ThunderFly-aerospace/Auto-G2/CAD/img/111_1009.png

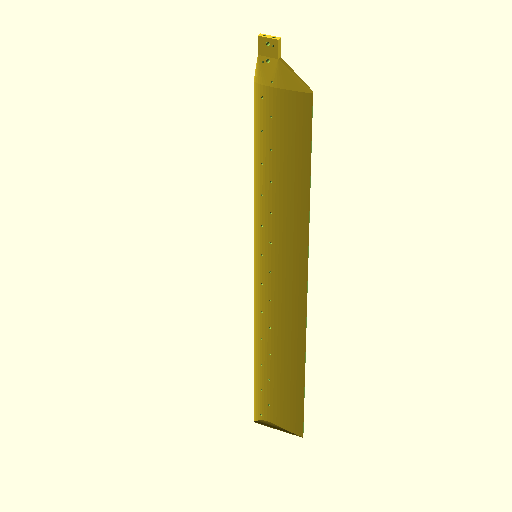
CAD/img/111_1009.png
