ThunderFly-aerospace/Auto-G2/CAD/img/888_1010.png

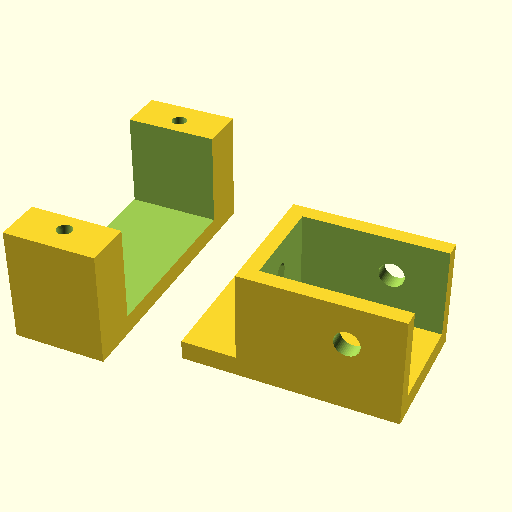
CAD/img/888_1010.png
