ThunderFly-aerospace/Auto-G2/doc/img/111_1001.png

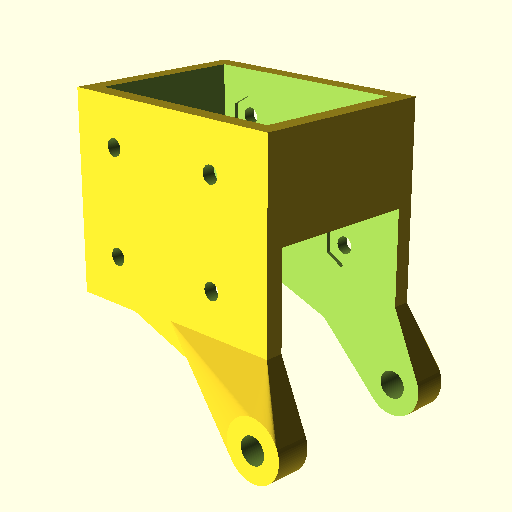
doc/img/111_1001.png
