ThunderFly-aerospace/Auto-G2/doc/img/111_1002.png

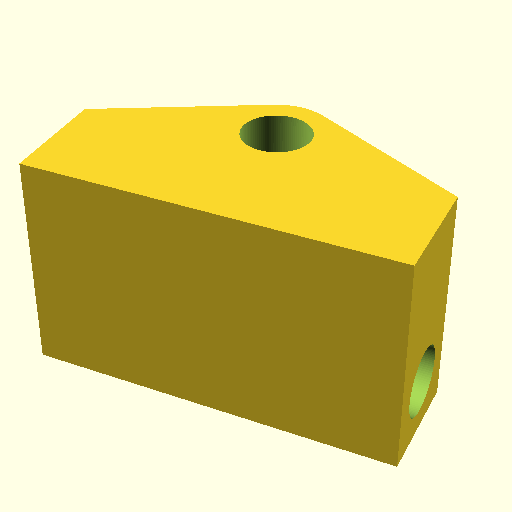
doc/img/111_1002.png
