ThunderFly-aerospace/Auto-G2/doc/img/111_1003.png

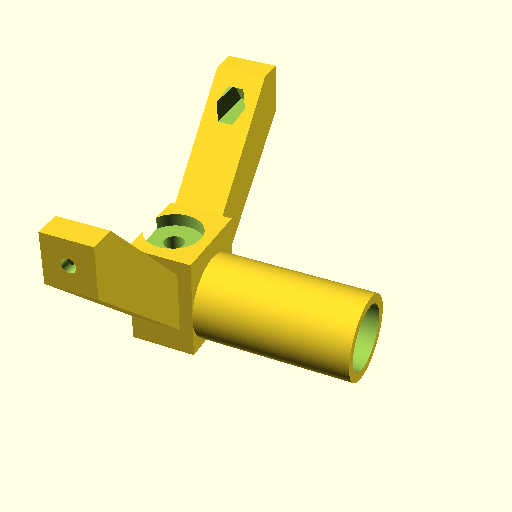
doc/img/111_1003.png
