ThunderFly-aerospace/Auto-G2/doc/img/111_1004.png

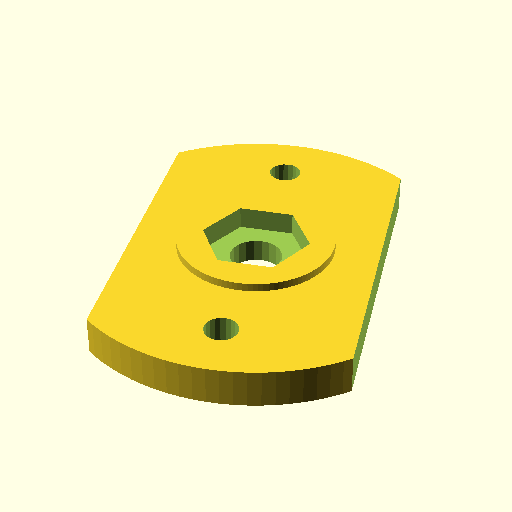
doc/img/111_1004.png
