ThunderFly-aerospace/Auto-G2/doc/img/111_1005.png

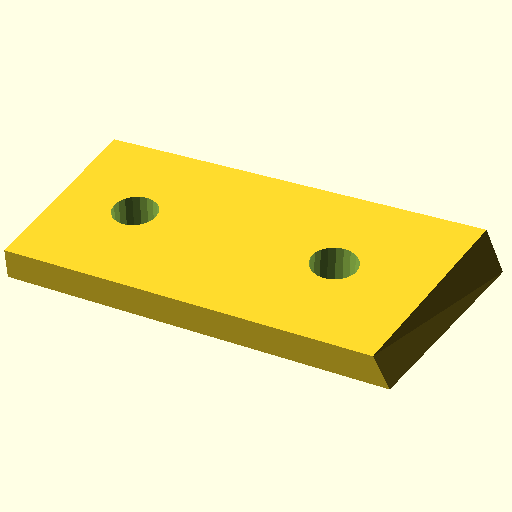
doc/img/111_1005.png
