ThunderFly-aerospace/Auto-G2/doc/img/111_1006.png

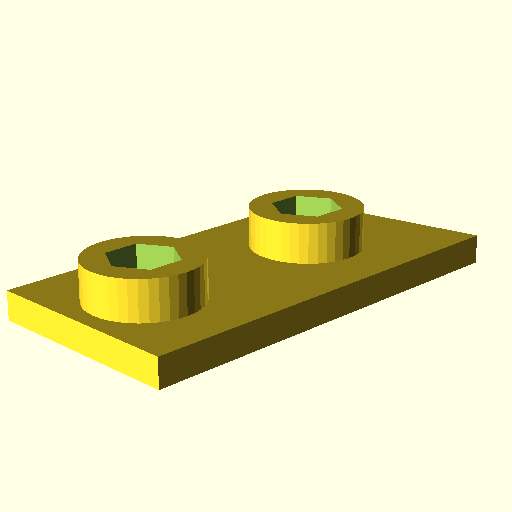
doc/img/111_1006.png
