ThunderFly-aerospace/Auto-G2/doc/img/111_1007.png

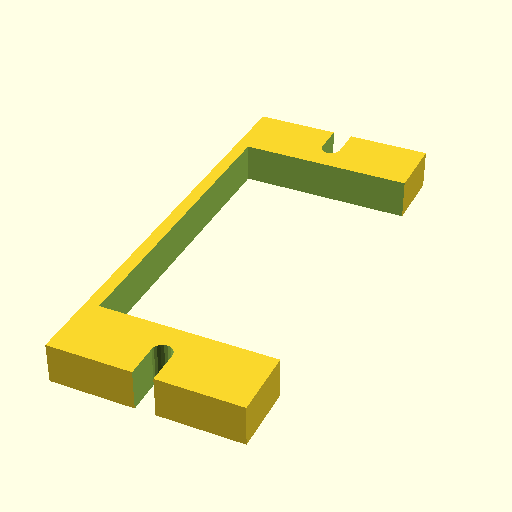
doc/img/111_1007.png
