ThunderFly-aerospace/Auto-G2/doc/img/111_1008.png

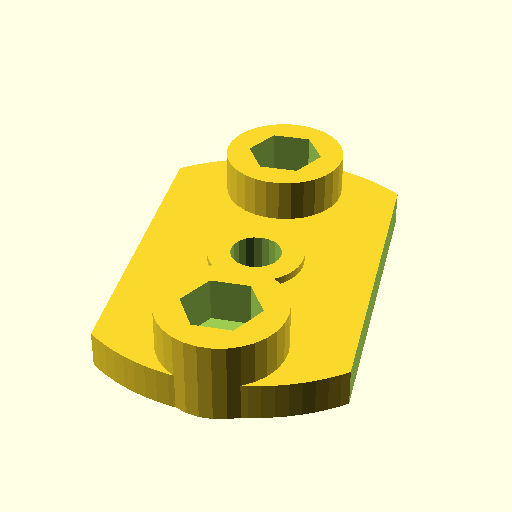
doc/img/111_1008.png
