ThunderFly-aerospace/Auto-G2/doc/img/111_1009.png

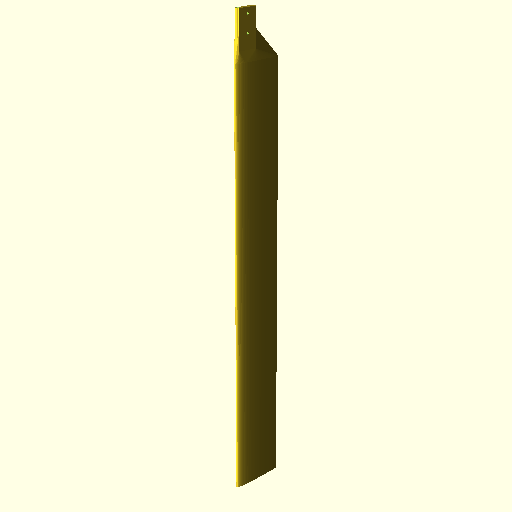
doc/img/111_1009.png
