ThunderFly-aerospace/Auto-G2/doc/img/111_1101.png

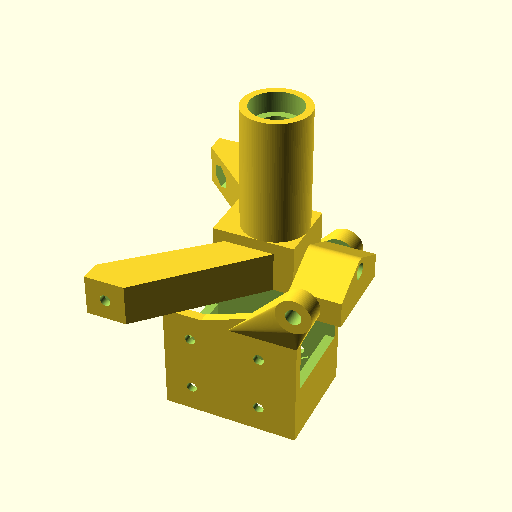
doc/img/111_1101.png
