ThunderFly-aerospace/Auto-G2/doc/img/111_1102.png

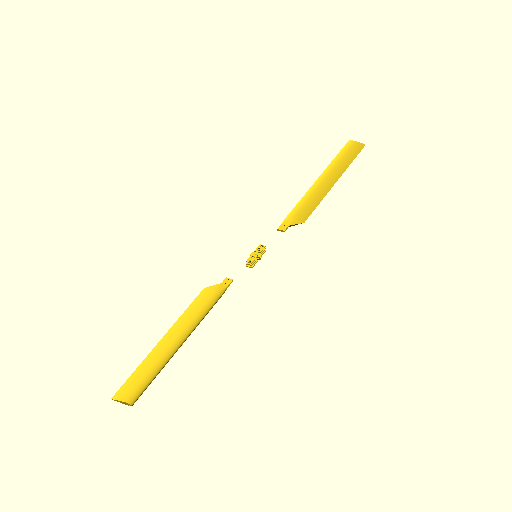
doc/img/111_1102.png
