ThunderFly-aerospace/Auto-G2/doc/img/888_1001.png

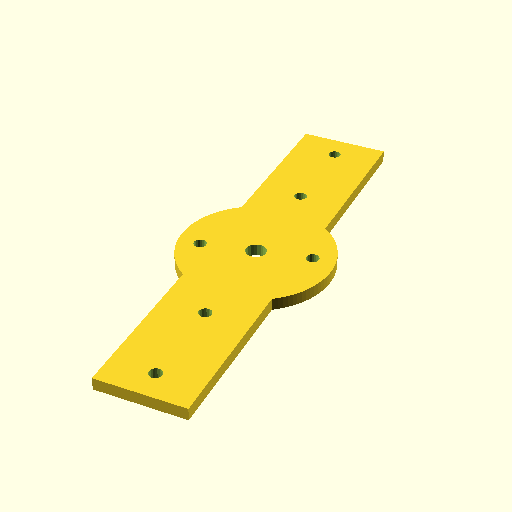
doc/img/888_1001.png
