ThunderFly-aerospace/Auto-G2/doc/img/888_1002.png

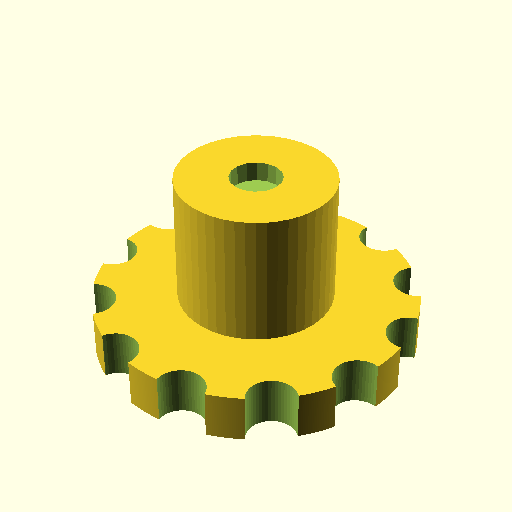
doc/img/888_1002.png
