ThunderFly-aerospace/Auto-G2/doc/img/888_1003.png

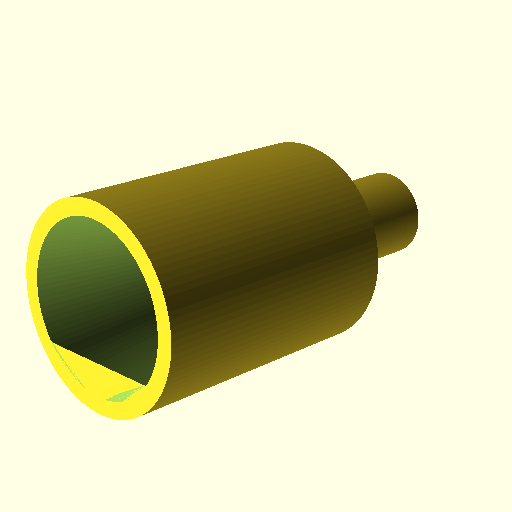
doc/img/888_1003.png
