ThunderFly-aerospace/Auto-G2/doc/img/888_1009.png

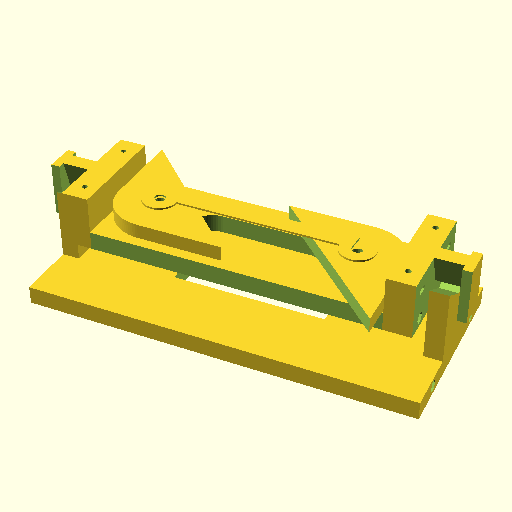
doc/img/888_1009.png
