ThunderFly-aerospace/Auto-G2/doc/img/888_1011.png

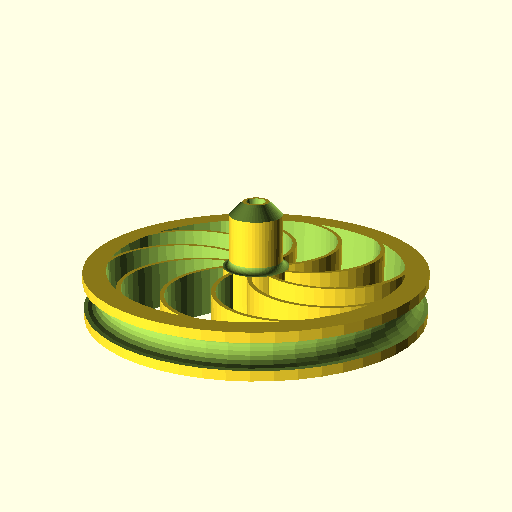
doc/img/888_1011.png
