ThunderFly-aerospace/Auto-G2/doc/img/20190310_154213.jpg

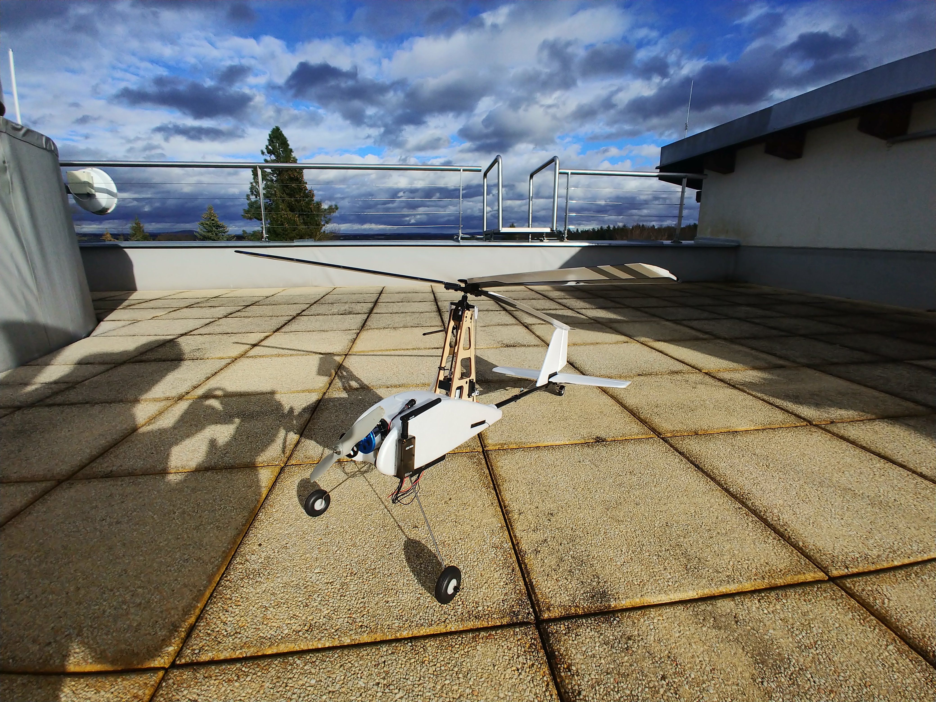
doc/img/20190310_154213.jpg
