ThunderFly-aerospace/Auto-G2/doc/wiki/meshlab_1.png

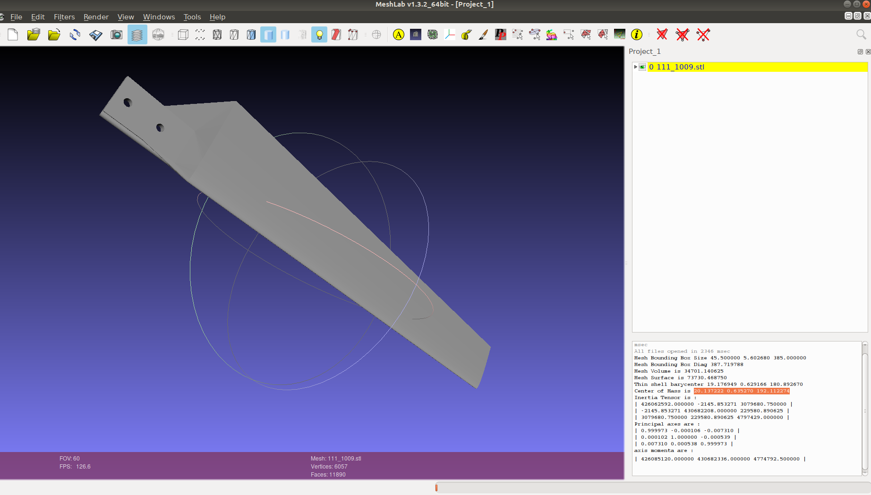
doc/wiki/meshlab_1.png
