ThunderFly-aerospace/Auto-G2/CAD/img/print_plate_rotor_parts.png

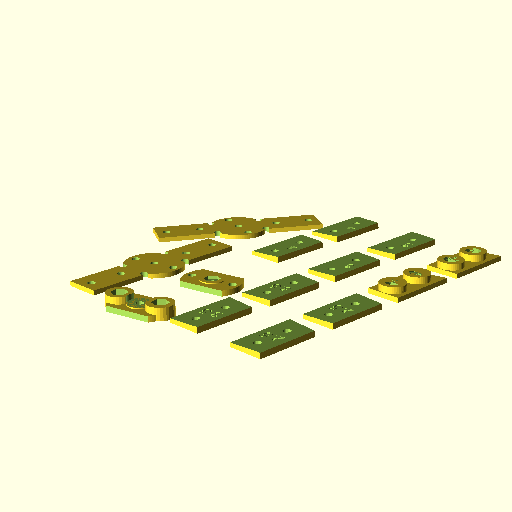
CAD/img/print_plate_rotor_parts.png
