ThunderFly-aerospace/Auto-G2/doc/img/111_1009_parts.png

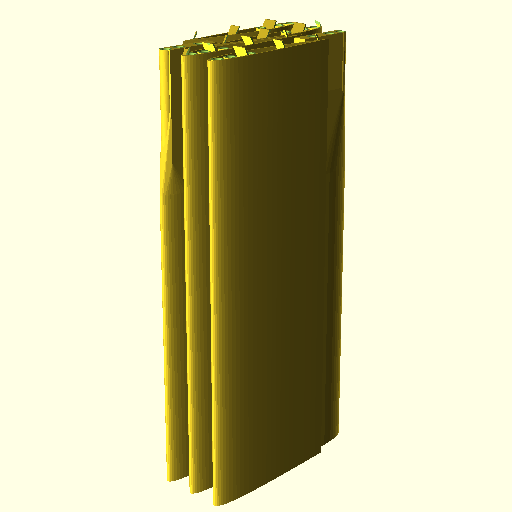
doc/img/111_1009_parts.png
