ThunderFly-aerospace/Auto-G2/doc/img/print_plate_blades_parts.png

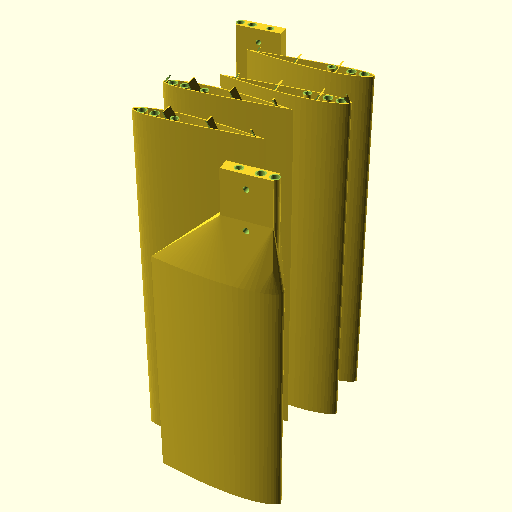
doc/img/print_plate_blades_parts.png
