ThunderFly-aerospace/Auto-G2/CAD/stl/print_plate_888_1001.stl

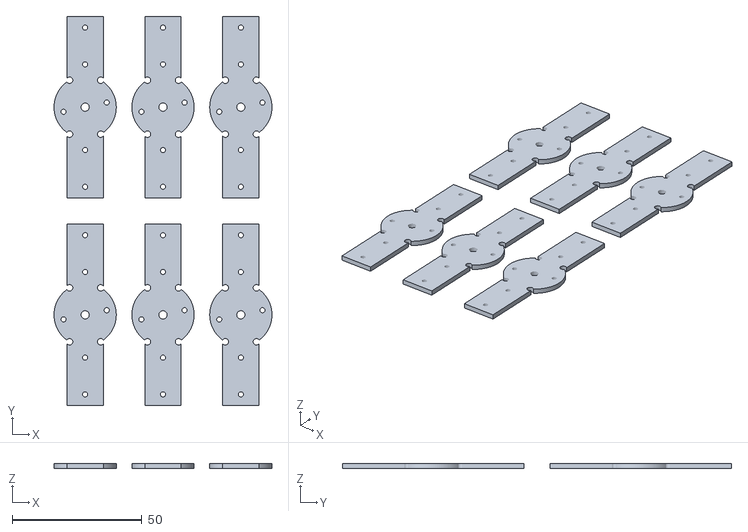
[picture p41: CAD file, 2019-07-24]
CAD/stl/print_plate_888_1001.stl
84.0 x 150.0 x 1.90
