ThunderFly-aerospace/Auto-G2/CAD/stl/888_1011.stl

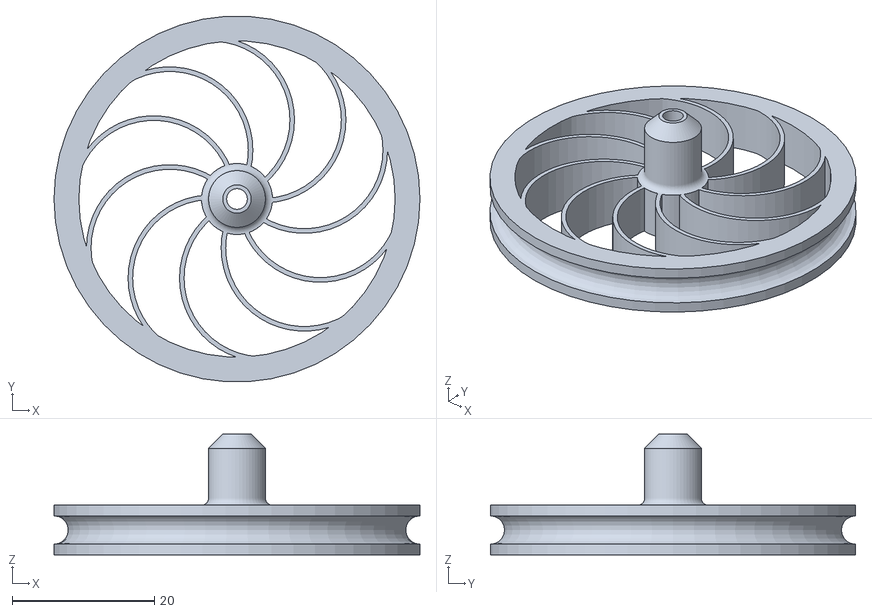
[picture p42: CAD file, 2019-07-24]
CAD/stl/888_1011.stl
51.5 x 51.4 x 17.0
