ThunderFly-aerospace/Auto-G2/CAD/stl/111_1006.stl

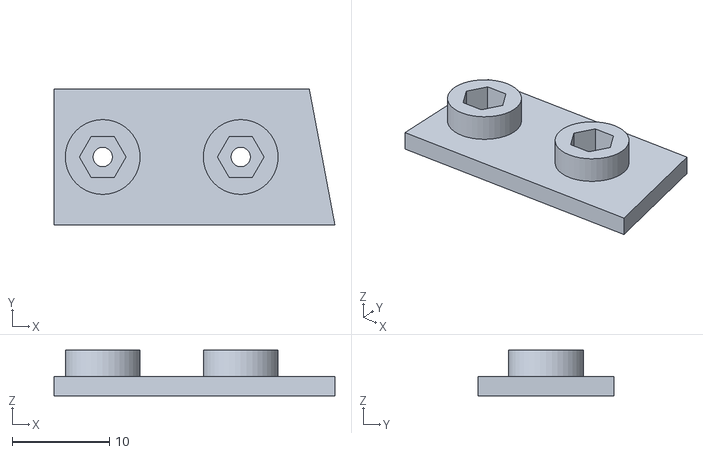
[picture p43: CAD file, 2019-07-04]
CAD/stl/111_1006.stl
28.8 x 14.0 x 4.67
