ThunderFly-aerospace/Auto-G2/CAD/stl/888_1001.stl

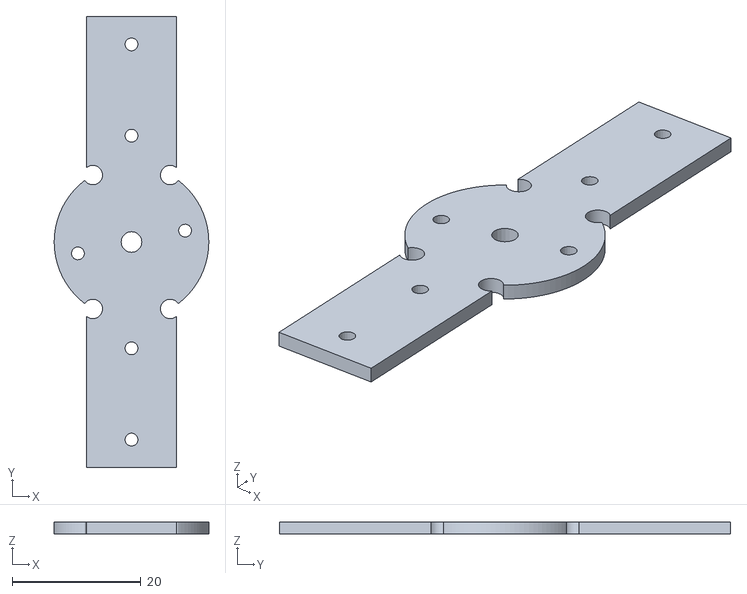
[picture p44: CAD file, 2019-07-04]
CAD/stl/888_1001.stl
24.0 x 70.0 x 1.90
