ThunderFly-aerospace/Auto-G2/CAD/stl/111_1101.stl

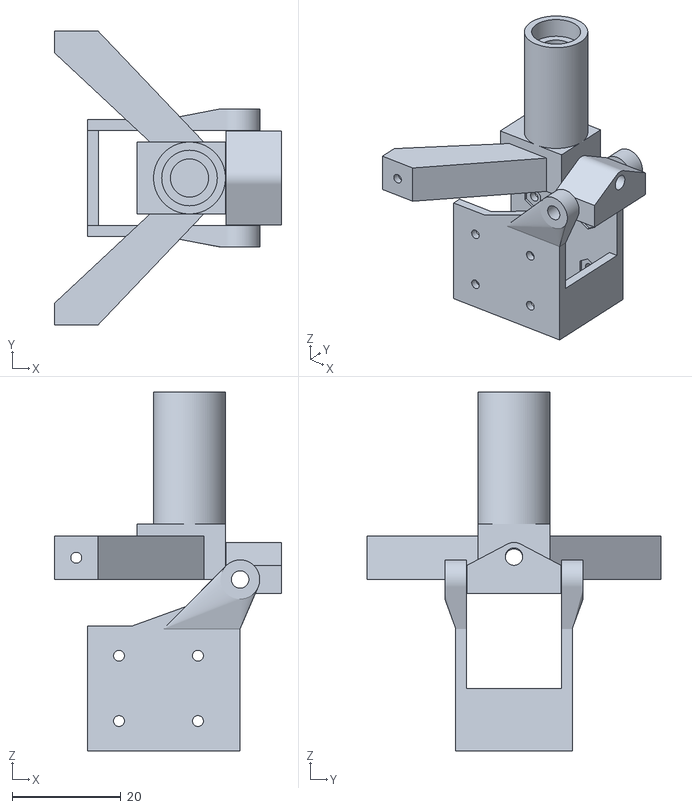
[picture p45: CAD file, 2019-07-04]
CAD/stl/111_1101.stl
41.7 x 54.0 x 65.9
