ThunderFly-aerospace/Auto-G2/CAD/STL/111_1009_parts.stl

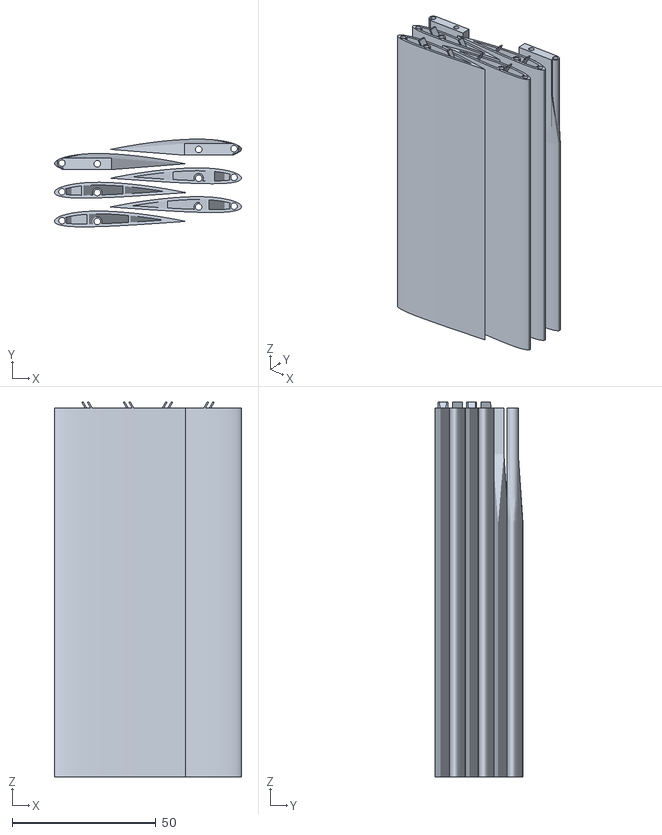
[picture p46: CAD file, 2019-06-12]
CAD/STL/111_1009_parts.stl
65.0 x 30.5 x 130.3
