ThunderFly-aerospace/Auto-G2/CAD/stl/888_1003.stl

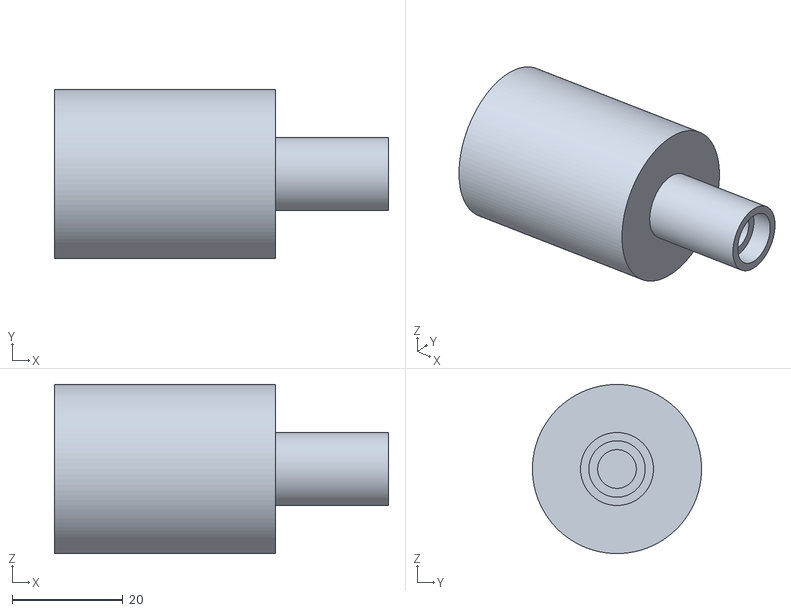
[picture p47: CAD file, 2019-05-24]
CAD/stl/888_1003.stl
60.4 x 30.6 x 30.6
