ThunderFly-aerospace/Auto-G2/CAD/stl/111_1003.stl

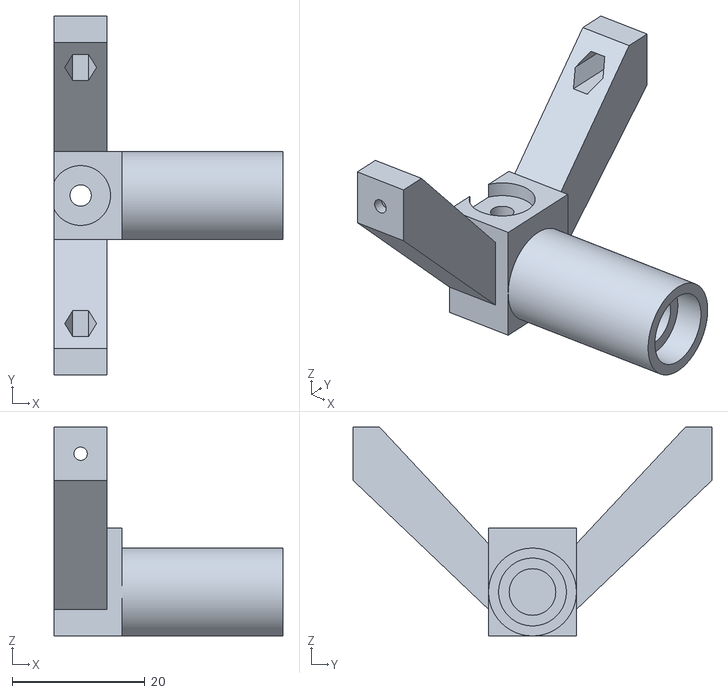
[picture p48: CAD file, 2019-05-24]
CAD/stl/111_1003.stl
34.4 x 54.0 x 31.4
