ThunderFly-aerospace/Auto-G2/CAD/stl/111_1001.stl

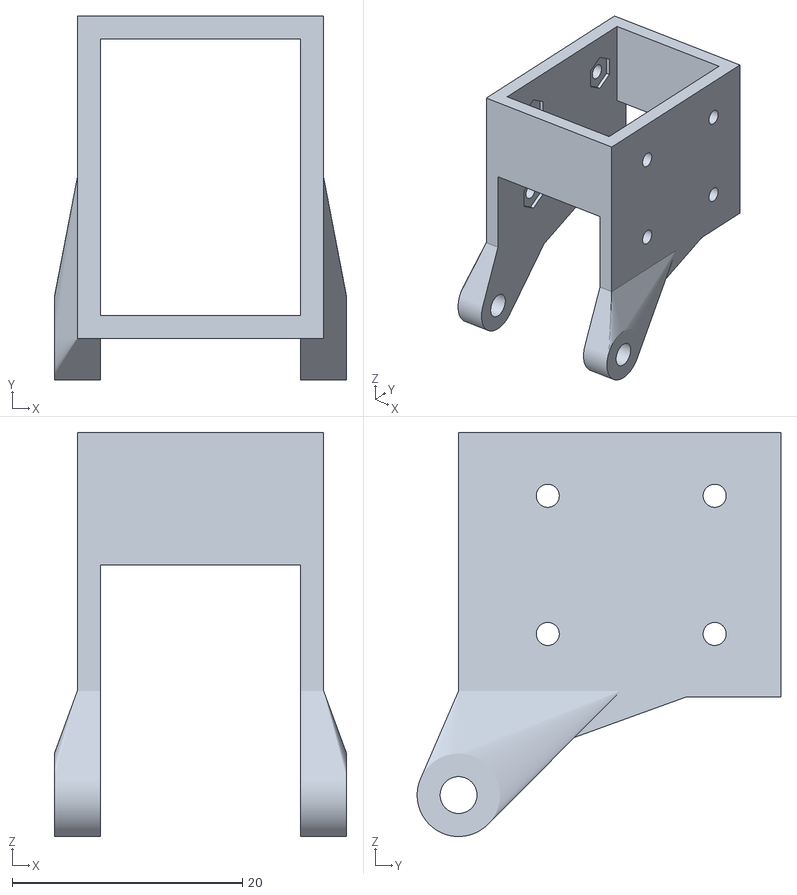
[picture p49: CAD file, 2019-05-24]
CAD/stl/111_1001.stl
25.4 x 31.6 x 35.1
