ThunderFly-aerospace/Auto-G2/CAD/stl/111_1005.stl

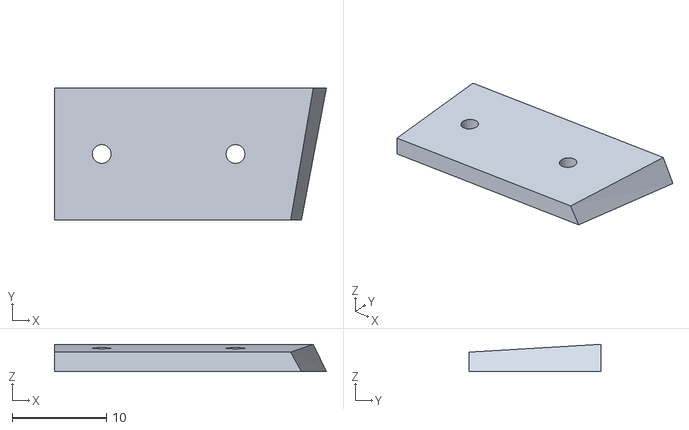
[picture p50: CAD file, 2019-05-24]
CAD/stl/111_1005.stl
28.8 x 14.0 x 2.90
