ThunderFly-aerospace/Auto-G2/CAD/stl/888_1002.stl

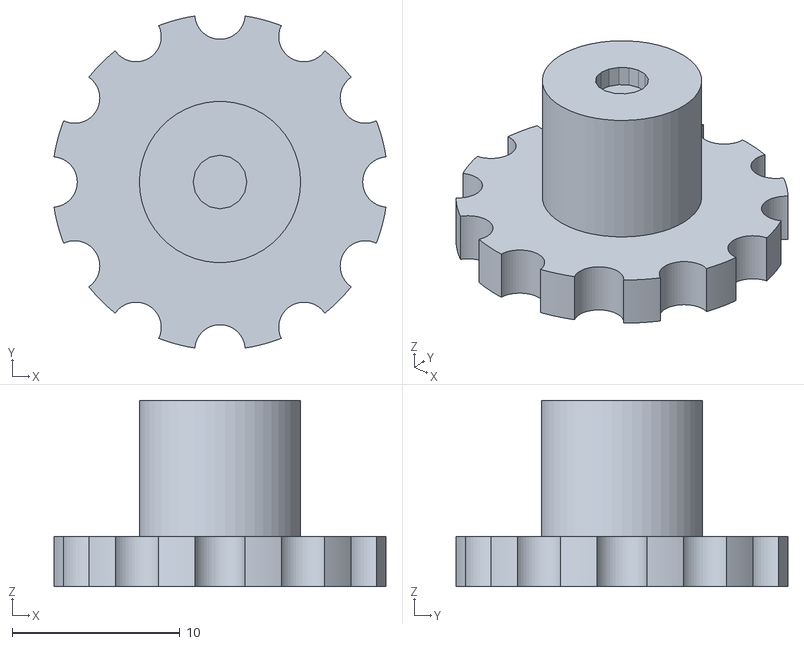
[picture p51: CAD file, 2019-05-06]
CAD/stl/888_1002.stl
19.8 x 19.8 x 11.1
