ThunderFly-aerospace/Auto-G2/CAD/stl/888_1009.stl

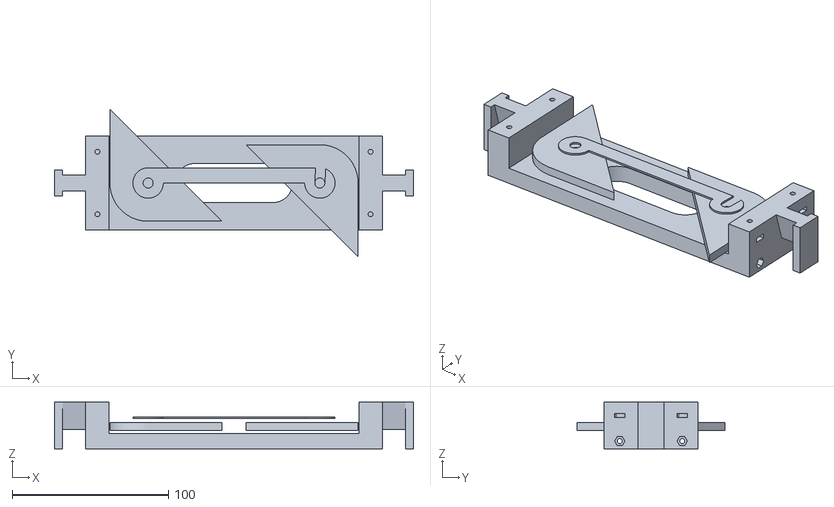
[picture p52: CAD file, 2019-05-06]
CAD/stl/888_1009.stl
230.0 x 94.7 x 30.0
