ThunderFly-aerospace/Auto-G2/CAD/stl/111_1007.stl

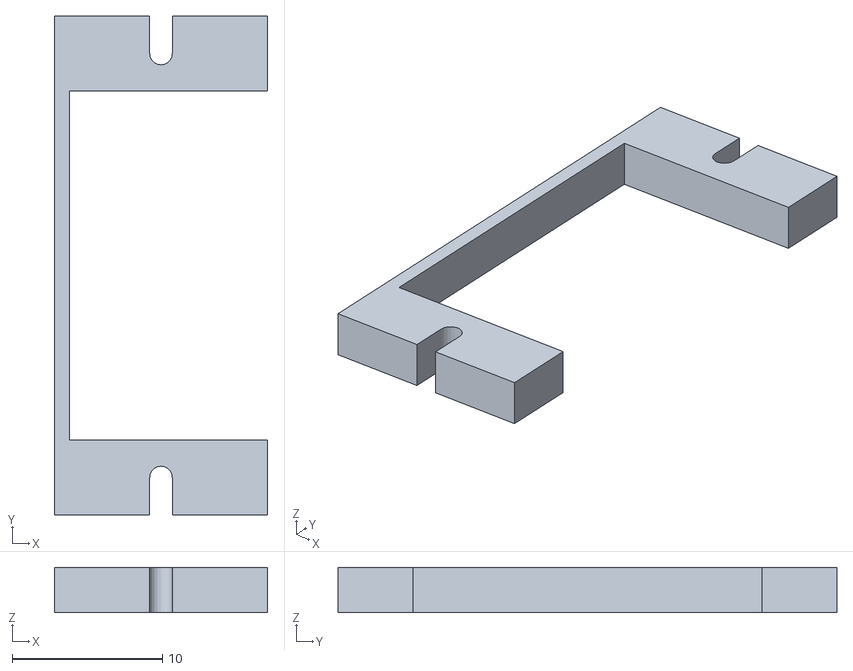
[picture p53: CAD file, 2019-04-24]
CAD/stl/111_1007.stl
14.2 x 33.2 x 3.00
