ThunderFly-aerospace/Auto-G2/CAD/STL/111_1102.stl

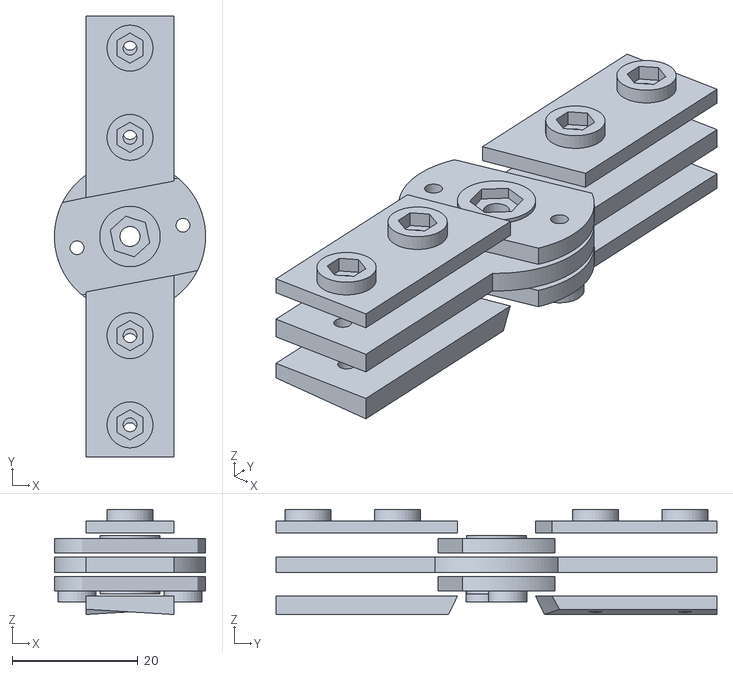
[picture p54: CAD file, 2019-04-24]
CAD/STL/111_1102.stl
24.0 x 70.0 x 16.7
