ThunderFly-aerospace/Auto-G2/CAD/stl/111_1002.stl

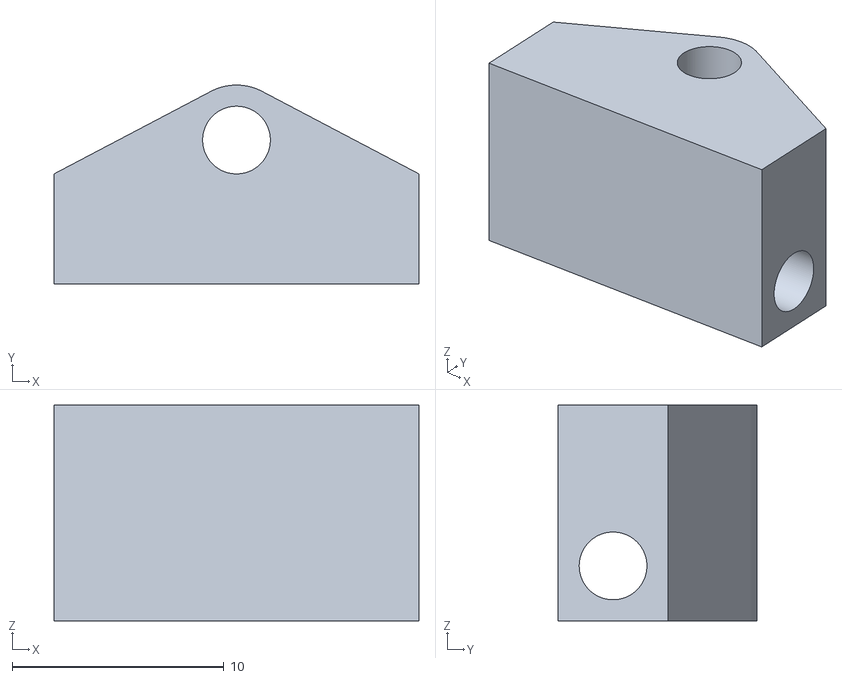
[picture p55: CAD file, 2019-03-27]
CAD/stl/111_1002.stl
17.2 x 9.40 x 10.2
