ThunderFly-aerospace/Auto-G2/CAD/src/888_1001.scad

//
//
//

include <../parameters.scad>

module 888_1001(hole_diameter=3)
{
    angle_between_blades = 360 / rotor_blades_count;
    rotor_center_plate_size = 30;
    rotor_mounting_plate_size = 20;
    shaft_diameter = M3_screw_diameter;
    thickness = 1.9;
    blade_screws_distance = (16.47+11.86)/2;

    translate([0, 0, thickness/2])
    difference () {
        union () {
            cylinder(r = 3+9, h = thickness, center = true, $fn = 100);

            for (i = [0:rotor_blades_count]){
                rotate([0,0, i*angle_between_blades])
                    translate([0, 20, 0])
                        cube([14, 30, thickness], center = true);
            }
        }

        cylinder(d = shaft_diameter, h = 2* thickness, center = true, $fn = 20);


        for (i = [1:rotor_blades_count]){
            rotate([0,0, i*angle_between_blades])
                translate([0, 16.5 + blade_screws_distance/2, 0]) {
                    translate([0, blade_screws_distance/2, 0])
                        cylinder(d = blade_mount_screw, h = 2* thickness, center = true, $fn = 20);
                    translate([0, -blade_screws_distance/2, 0])
                        cylinder(d = blade_mount_screw, h = 2* thickness, center = true, $fn = 20);
                }
        }

        rotate([0,0, rotor_delta_angle])
        for (i = [1:rotor_blades_count]){
            rotate([0,0, i*angle_between_blades + angle_between_blades/2])
                translate([0, 3 + 4.5 + blade_mount_screw/2, 0])
                    cylinder(d = blade_mount_screw, h = 2* thickness, center = true, $fn = 20);
        }

        //diry pro lepsi moznost utrzeni listu
        for (i=[1,2,4,5]) {
            rotate ([0, 0, 60*i])
                translate ([12, 0, 0])
                    cylinder (h=thickness+2, d=hole_diameter, center=true, $fn=100);
        }
    }
}

888_1001();
