ThunderFly-aerospace/Auto-G2/CAD/src/4printing/print_plate_111_1009_parts.scad

include <../../parameters.scad>
use <../111_1009.scad>

//@set_slicing_config(../../slicing/blades/blade.ini)

//@set_modificator(modificator)
//@set_slicing_config(../../slicing/blades/infill_modif.ini, modificator)

//@set_modificator(modificatorb)
//@set_slicing_config(../../slicing/blades/ends_modif.ini, modificatorb)




rotate([180, 0, 0])
    translate([0, 20, -rotor_blade_length/3])
        111_1009_print(1);

    111_1009_print(2);

translate([0, 20, 0])
    111_1009_print(3);

translate([60, 12, 0])
    rotate([0, 0, 180]){
        rotate([180, 0, 0])
            translate([0, 20, -rotor_blade_length/3])
                111_1009_print(1);
            111_1009_print(2);
        translate([0, 20, 0])
            111_1009_print(3);
    }

module modificator(){
/* union(){
    translate([0, -20, 0])
        111_1009_print_modificator(1);

        111_1009_print_modificator(2);

    translate([0, 20, 0])
        111_1009_print_modificator(3);

    translate([60, 12, 0])
    rotate([0, 0, 180]){
        translate([0, -20, 0])
            111_1009_print_modificator(1);
            111_1009_print_modificator(2);
        translate([0, 20, 0])
            111_1009_print_modificator(3);
    }
} */

rotate([180, 0, 0])
    translate([0, 20, -rotor_blade_length/3])
        111_1009_print_modificator(1);

    111_1009_print_modificator(2);

translate([0, 20, 0])
    111_1009_print_modificator(3);

translate([60, 12, 0])
    rotate([0, 0, 180]){
        rotate([180, 0, 0])
            translate([0, 20, -rotor_blade_length/3])
                111_1009_print_modificator(1);
            111_1009_print_modificator(2);
        translate([0, 20, 0])
            111_1009_print_modificator(3);
    }
}

module modificatorb(){
/* union(){
    translate([0, -20, 0])
        111_1009_end_print_modificator(1);

        111_1009_end_print_modificator(2);

    translate([0, 20, 0])
        111_1009_end_print_modificator(3);

    translate([60, 12, 0])
    rotate([0, 0, 180]){
        translate([0, -20, 0])
            111_1009_end_print_modificator(1);
            111_1009_end_print_modificator(2);
        translate([0, 20, 0])
            111_1009_end_print_modificator(3);
    }
} */
rotate([180, 0, 0])
    translate([0, 20, -rotor_blade_length/3])
        111_1009_end_print_modificator(1);

    111_1009_end_print_modificator(2);

translate([0, 20, 0])
    111_1009_end_print_modificator(3);

translate([60, 12, 0])
    rotate([0, 0, 180]){
        rotate([180, 0, 0])
            translate([0, 20, -rotor_blade_length/3])
                111_1009_end_print_modificator(1);
            111_1009_end_print_modificator(2);
        translate([0, 20, 0])
            111_1009_end_print_modificator(3);
    }
}

%modificator();
%modificatorb();
