ThunderFly-aerospace/Auto-G2/CAD/src/4printing/print_plate_888_1011.scad

use <../888_1011.scad>


888_1011();

translate([55, 0, 0])
mirror([1, 0, 0])
888_1011();
