ThunderFly-aerospace/Auto-G2/CAD/src/4printing/print_plate_rotor_parts.scad

use <../888_1001.scad>
use <../111_1004.scad>
use <../111_1005.scad>
use <../111_1006.scad>
use <../111_1008.scad>

use <../lib/stdlib/shortcuts.scad>

place_in_rect(35, 30) // arange that stuff in a grid
{
    111_1008();
    111_1004();

   
    111_1005(4);
    111_1005(4);

    111_1005(3.5);
    111_1005(3.5);
    
    111_1005(3);
    111_1005(3);
    
    111_1005(2.5);
    111_1005(2.5);

    111_1006();
    111_1006();

}
    
translate([-20, 60, 0])
    rotate(90)
        888_1001();

translate([35, 70, 0])
    rotate(90-30)
        888_1001();
