ThunderFly-aerospace/Auto-G2/doc/img/print_plate_888_1001.png

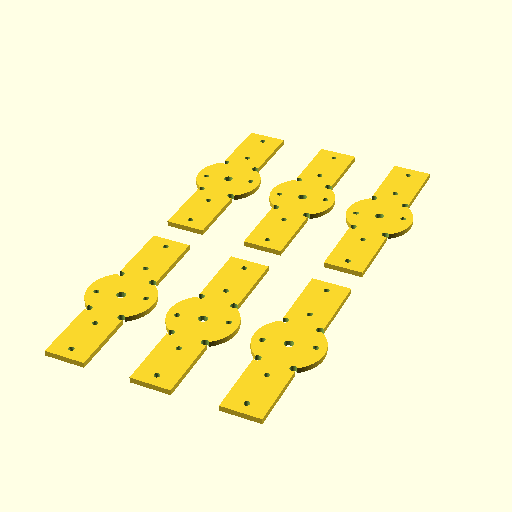
doc/img/print_plate_888_1001.png
