ThunderFly-aerospace/Auto-G2/doc/img/print_plate_888_1001_2,5.png

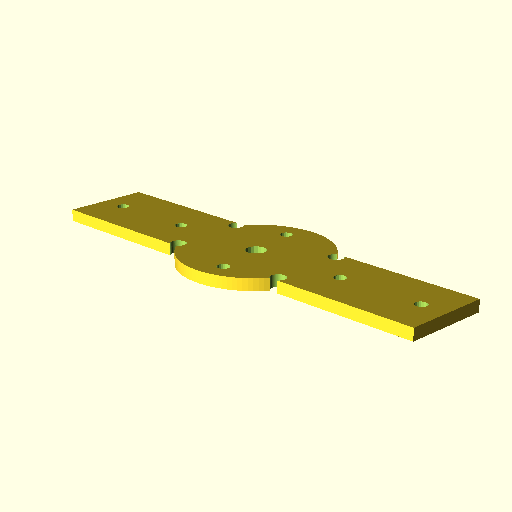
doc/img/print_plate_888_1001_2,5.png
