ThunderFly-aerospace/Auto-G2/doc/img/print_plate_888_1009_cradle.png

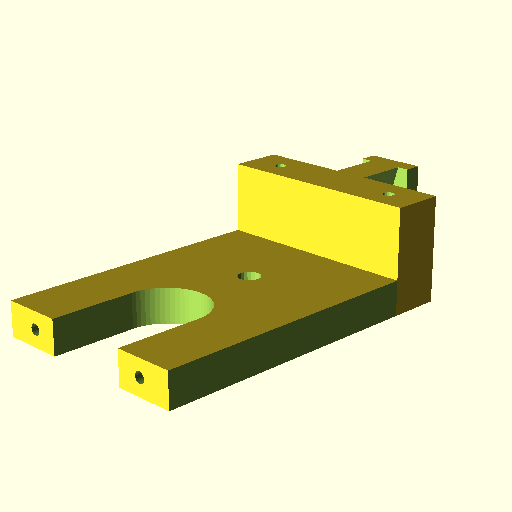
doc/img/print_plate_888_1009_cradle.png
