ThunderFly-aerospace/Auto-G2/doc/img/print_plate_888_1009_scale.png

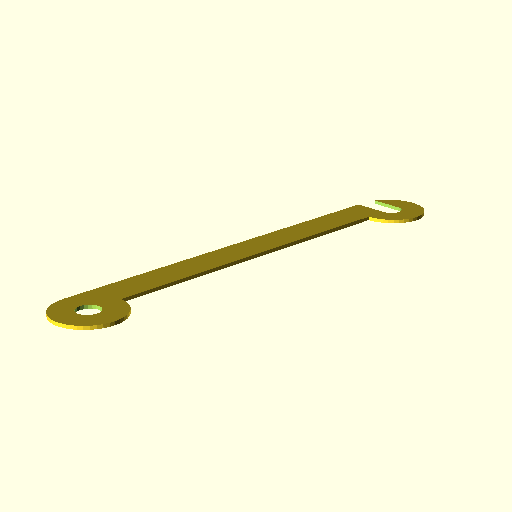
doc/img/print_plate_888_1009_scale.png
