ThunderFly-aerospace/Auto-G2/doc/img/print_plate_888_1011.png

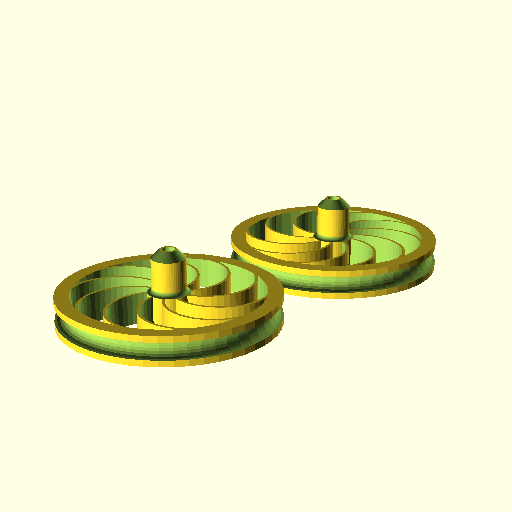
doc/img/print_plate_888_1011.png
