ThunderFly-aerospace/Auto-G2/doc/img/print_plate_1009_scale.png

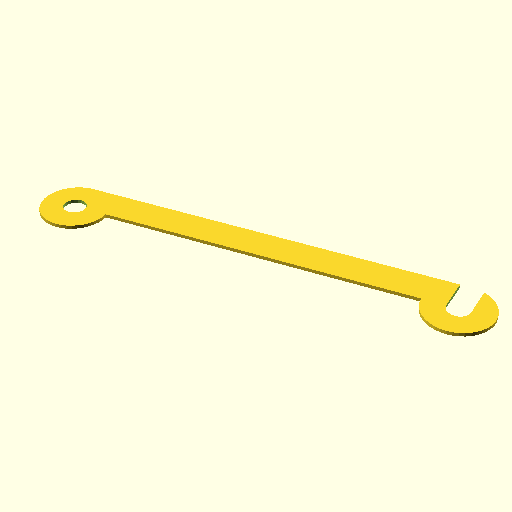
doc/img/print_plate_1009_scale.png
