ThunderFly-aerospace/Auto-G2/doc/img/print_plate_1009_shapeB.png

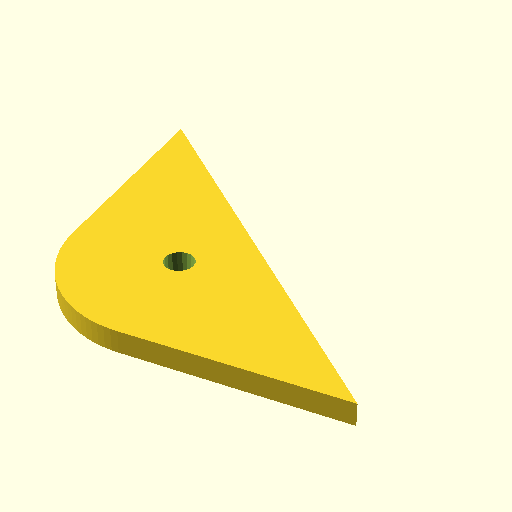
doc/img/print_plate_1009_shapeB.png
